IvanSamardzic/NetWork-Sense/hardware-tests/ultrasonic-sensor-tests/ultrasonic-sensor-testing.ino

const int trigPin = 9;
const int echoPin = 10;
int duration, distance;

void setup() {
  Serial.begin(9600);
  pinMode(trigPin, OUTPUT);
  pinMode(echoPin, INPUT);
}

void loop() {
  digitalWrite(trigPin, LOW);
  delayMicroseconds(2);
  digitalWrite(trigPin, HIGH);
  delayMicroseconds(10);
  digitalWrite(trigPin, LOW);
  duration = pulseIn(echoPin, HIGH);
  distance = duration * 0.034 / 2;
  Serial.print("Distance: ");
  Serial.println(distance);
}
